lwolf/srvant-board/kicad/mk2/srvant-mk2/3D/RJ45-c-5-2337992-3-a-3d.stp

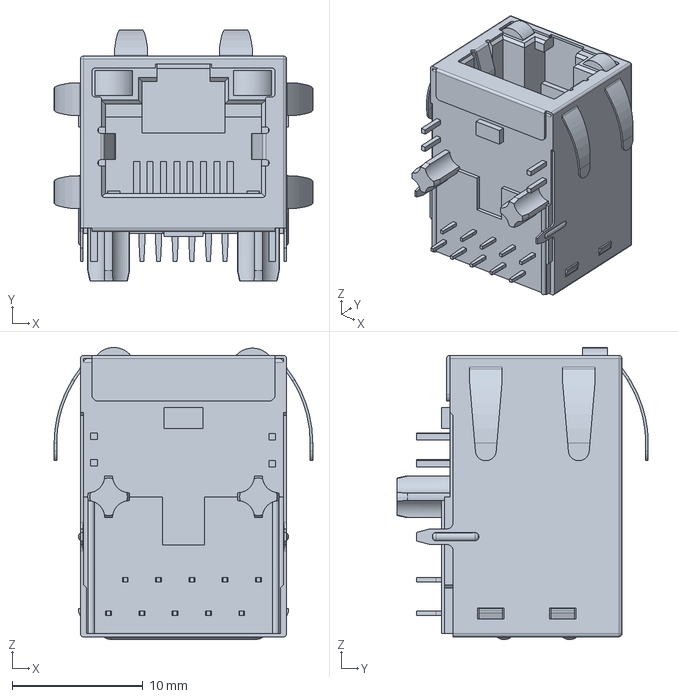
[picture p17: CAD file, 2021-07-14]
kicad/mk2/srvant-mk2/3D/RJ45-c-5-2337992-3-a-3d.stp
19.8 x 19.2 x 22.3 mm
