lwolf/srvant-board/kicad/mk2/srvant-mk2/3D/TLV62585DRLR-DRL0006A.stp

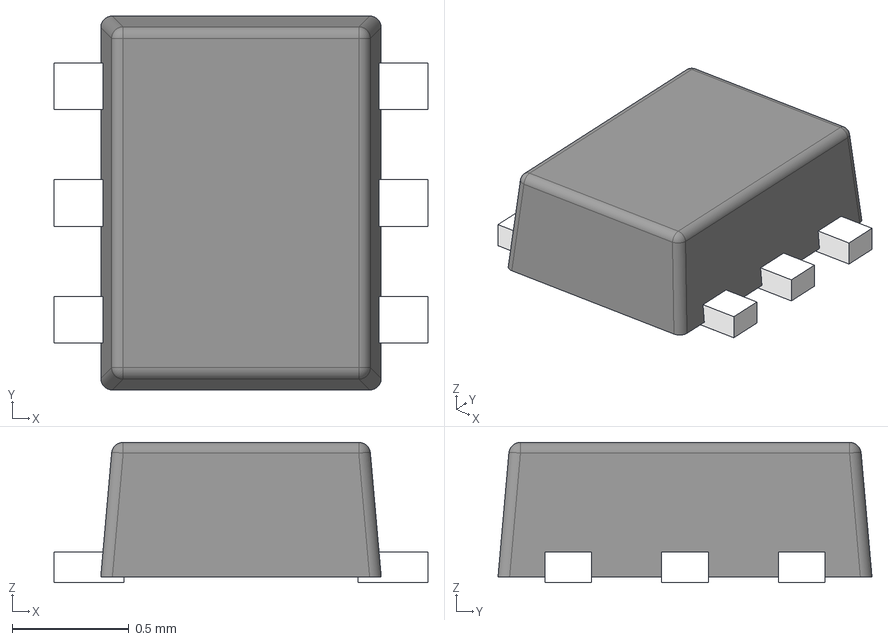
[picture p18: CAD file, 2021-07-14]
kicad/mk2/srvant-mk2/3D/TLV62585DRLR-DRL0006A.stp
1.60 x 1.60 x 0.6 mm
FRAME-DRL0006A
BODY-SOT
PIN1-ID
