lwolf/srvant-board/kicad/mk2/srvant-mk2/3D/m2-2199230-5-b2-3d.stp

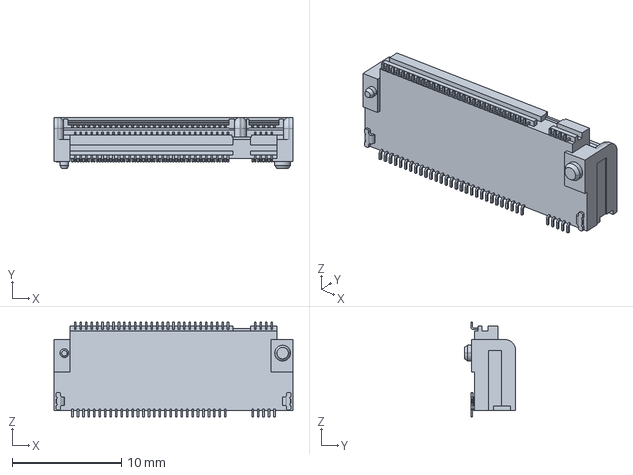
[picture p19: CAD file, 2021-07-14]
kicad/mk2/srvant-mk2/3D/m2-2199230-5-b2-3d.stp
21.9 x 4.70 x 8.70 mm
